afonsus1997/Eurorack-Modular-Synth/Modules/VCO/Simulations/CV_in.asc

C1: cap; 500p
R1: res; 100k
R2: res; 41.2k
R3: res; 24.9k
R4: res; 100k
R5: res; 24.9k
R6: res; 100k
R7: res; 41.2k
R8: res; 24.9k
R9: res; 24.9k
U1: opamp2; TL072
U2: opamp2; TL072
U3: opamp2; TL072
U4: opamp2; TL072
V1: voltage; 12
V2: voltage; 12
V3: voltage; SINE(5 5 1); AC 10
V5: voltage; 3.3
V7: voltage; SINE(5 5 1); AC 10
Vsweep1: voltage; ""; AC 1
Vsweep2: voltage; ""; AC 1
Named nets: 0, VCC, VEE, 3v3, out, out_nocap
.inc TL072.mod
.ac dec 10000 10 1G
.tran 0 5 0 100m
.inc TL072.mod
