afonsus1997/Eurorack-Modular-Synth/Modules/VCO/Simulations/FM_in.asc

C1: cap; 1n
R1: res; 100k
R2: res; 41.2k
R3: res; 24.9k
R4: res; 100k
R5: res; 24.9k
R6: res; 120k
R7: res; 200k
R8: res; 100k
U1: opamp2; TL072
U2: opamp2; TL072
V1: voltage; 12
V2: voltage; 12
V3: voltage; SINE(0 5 1); AC 10
V4: voltage; -0; AC 0
V5: voltage; 5
Vsweep1: voltage; ""; AC 1
Named nets: 0, VCC, VEE, adj
.inc TL072.mod
;ac dec 10000 10 1G
.tran 0 5 0 100m
