afonsus1997/Eurorack-Modular-Synth/Modules/VCO/Simulations/DAC_output.asc

C1: cap; 1n
C2: cap; 3.9n
C3: cap; 10µ
C4: cap; 47p
C5: cap; 10µ
R1: res; 3k
R2: res; 5.6k
R3: res; 5.6k
R4: res; 20k
R5: res; 100k
R6: res; 1k
R7: res; 100k
R8: res; 30k
U1: opamp2; NE5532TI_SN
U2: opamp2; NE5532TI_SN
V1: voltage; 12
V2: voltage; 12
V3: voltage; SINE(2.5 2.5 5k); AC 0
Vsweep1: voltage; ""; AC 1
Named nets: 0, VCC, VEE
.inc NE5532_SN.mod
.tran 0 1m 0 10n
.ac dec 10000 10 1G
.four 5000 10 100 V(n002)
.options numdgt = 7
.options plotwinsize = 0
