afonsus1997/Eurorack-Modular-Synth/Modules/VCO/Simulations/DAC_output_vcom.asc

C1: cap; 1n
C2: cap; 6.2n
C3: cap; 10µ
C4: cap; 47p
R1: res; 2.2k
R2: res; 4.7k
R3: res; 2.4k
R4: res; 18k
R5: res; 100k
R6: res; 1k
R7: res; 100k
R8: res; 30k
U1: opamp2; NE5532TI_SN
U2: opamp2; NE5532TI_SN
V1: voltage; SINE(2.5 2.5 5k); AC 0
V2: voltage; 12
V3: voltage; 12
V4: voltage; 2.5; AC 0
Vsweep: voltage; ""; AC 1
Named nets: 0, VCC, VEE
.inc NE5532_SN.mod
.tran 0 1m 0 10n
.ac dec 10000 10 1G
.four 5000 10 100 V(n002)
.options numdgt = 7
.options plotwinsize = 0
