afonsus1997/Eurorack-Modular-Synth/Modules/VCO/Firmware/Minimal/Src/interfaces.h

/**
**********************************************************************************************************************************************************************************************************************************
* @file:	interfaces.h
* @author:	Afonso Muralha
* @date:	2020年07月20日 21:11:38 Monday
* @brief:	
**********************************************************************************************************************************************************************************************************************************
**/

#ifndef INTERFACES_H
#define INTERFACES_H

#include "stm32f1xx_hal.h"
#include "main.h"

enum jackList_e
{
    GateJack = 0,
    FMJack = 2,
    CVJack = 3,
    PWMJack = 1,
    Out1Jack = 4,
    Out2Jack = 5
};



void updateJackStatus();

void updateJackLEDs();

#endif
