afonsus1997/Eurorack-Modular-Synth/Modules/VCO/Firmware/Minimal/Src/inputProcessing.c

/**
**********************************************************************************************************************************************************************************************************************************
* @file:	inputProcessing.c
* @author:	Afonso Muralha
* @date:	2020年07月04日 23:36:21 Saturday
* @brief:	
**********************************************************************************************************************************************************************************************************************************
**/

#include "inputProcessing.h"
