afonsus1997/Eurorack-Modular-Synth/Modules/VCO/Firmware/Minimal/Src/inputProcessing.h

/**
**********************************************************************************************************************************************************************************************************************************
* @file:	inputProcessing.h
* @author:	Afonso Muralha
* @date:	2020年07月04日 23:36:34 Saturday
* @brief:	
**********************************************************************************************************************************************************************************************************************************
**/

#ifndef __INPUTPROCESSING_H
#define __INPUTPROCESSING_H

#include <math.h>

#endif
