afonsus1997/Eurorack-Modular-Synth/Modules/VCO/Firmware/Minimal/Src/wavetables.h

/**
**********************************************************************************************************************************************************************************************************************************
* @file:	wavetables.h
* @author:	Afonso Muralha
* @date:	2020年07月04日 02:32:41 Saturday
* @brief:	
**********************************************************************************************************************************************************************************************************************************
**/

#ifndef __WAVETABLES_H
#define __WAVETABLES_H

#include <stdint.h>

#endif // __WAVETABLES_H
